zhangjinke/Embedded-Tools-Hardware/Pictures/IMG_20241031_213614.jpg

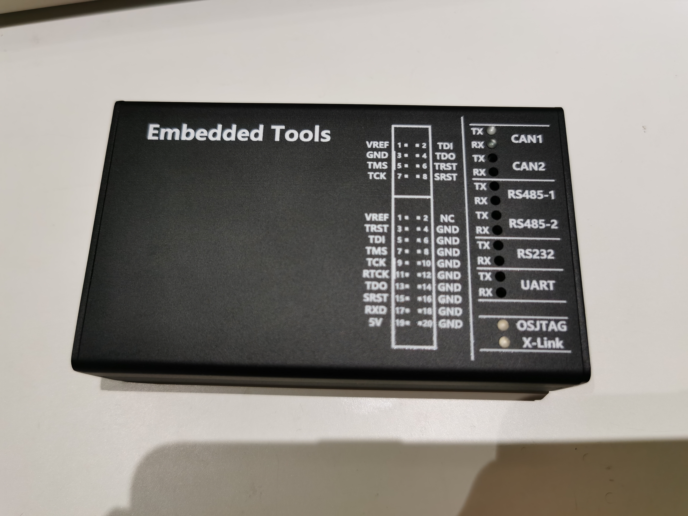
Pictures/IMG_20241031_213614.jpg
