zhangjinke/Embedded-Tools-Hardware/Pictures/IMG_20241031_214249.jpg

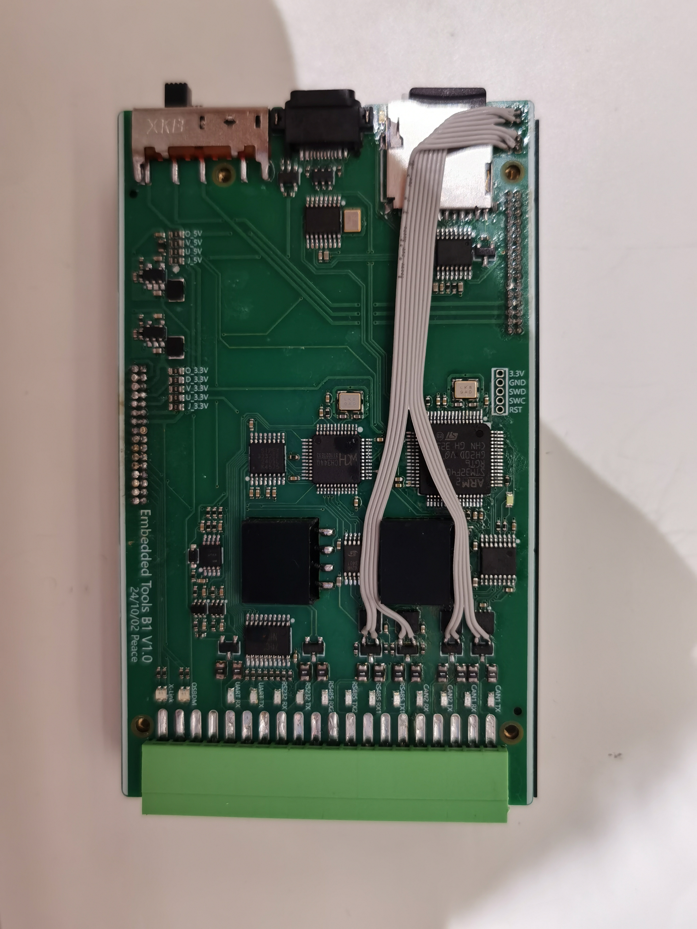
Pictures/IMG_20241031_214249.jpg
