zhangjinke/Embedded-Tools-Hardware/Pictures/IMG_20241031_214307.jpg

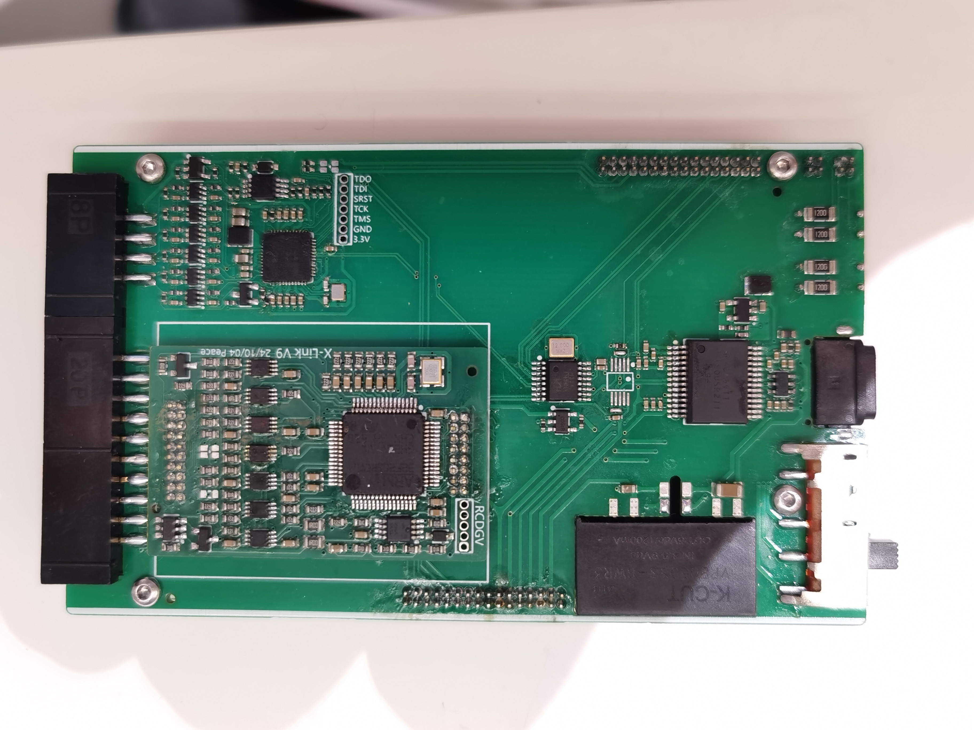
Pictures/IMG_20241031_214307.jpg
