zhangjinke/Embedded-Tools-Hardware/Pictures/IMG_20241031_214337.jpg

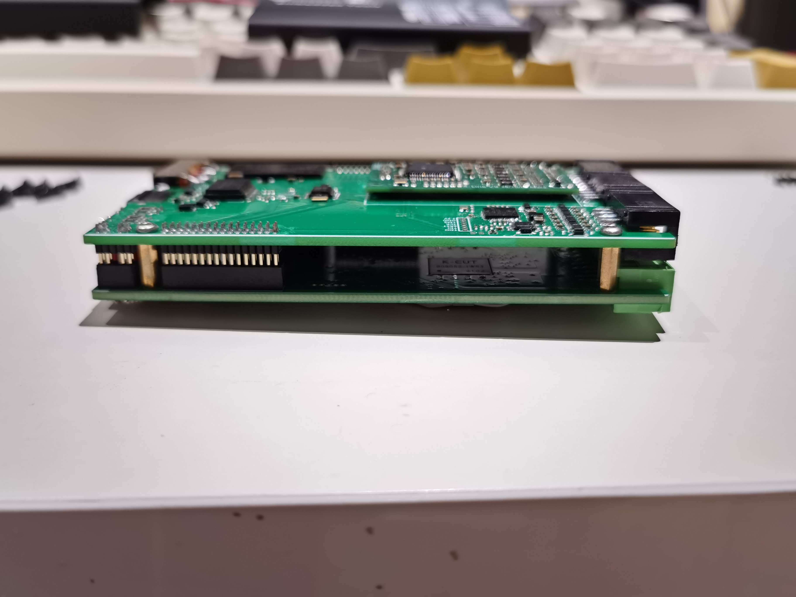
Pictures/IMG_20241031_214337.jpg
