zhangjinke/Embedded-Tools-Hardware/Pictures/IMG_20241110_171348.jpg

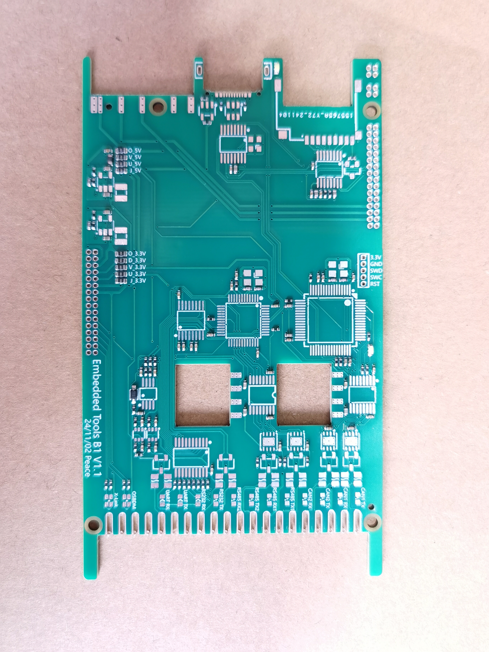
Pictures/IMG_20241110_171348.jpg
