zhangjinke/Embedded-Tools-Hardware/Pictures/IMG_20241110_171440.jpg

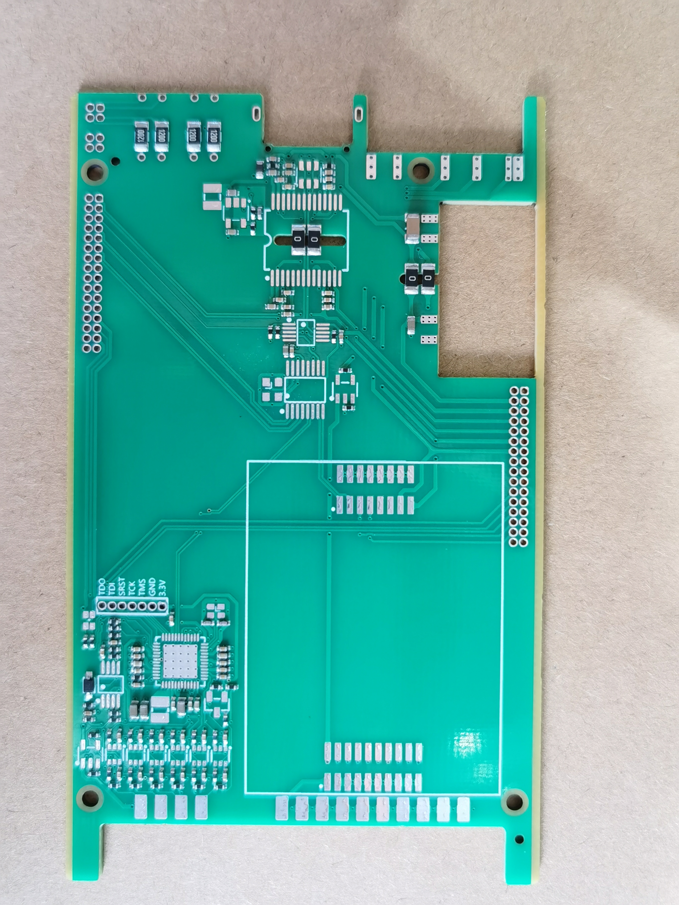
Pictures/IMG_20241110_171440.jpg
