zhangjinke/Embedded-Tools-Hardware/Pictures/IMG_20241111_111140.jpg

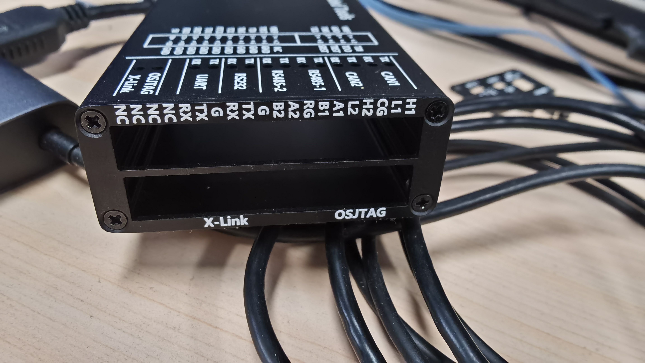
Pictures/IMG_20241111_111140.jpg
