zhangjinke/Embedded-Tools-Hardware/Pictures/IMG_20241116_104931.jpg

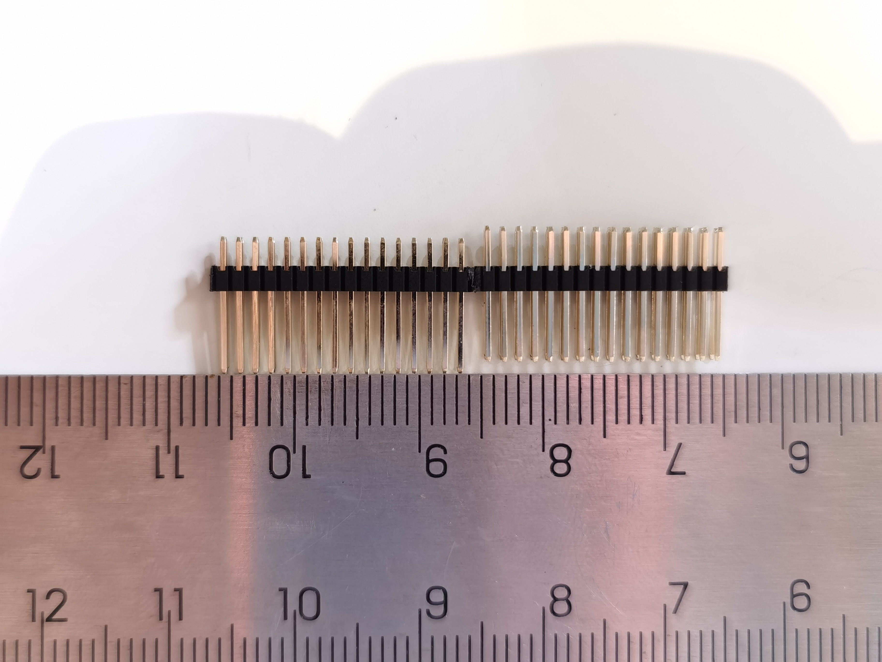
Pictures/IMG_20241116_104931.jpg
