zhangjinke/Embedded-Tools-Hardware/Pictures/IMG_20241116_105723.jpg

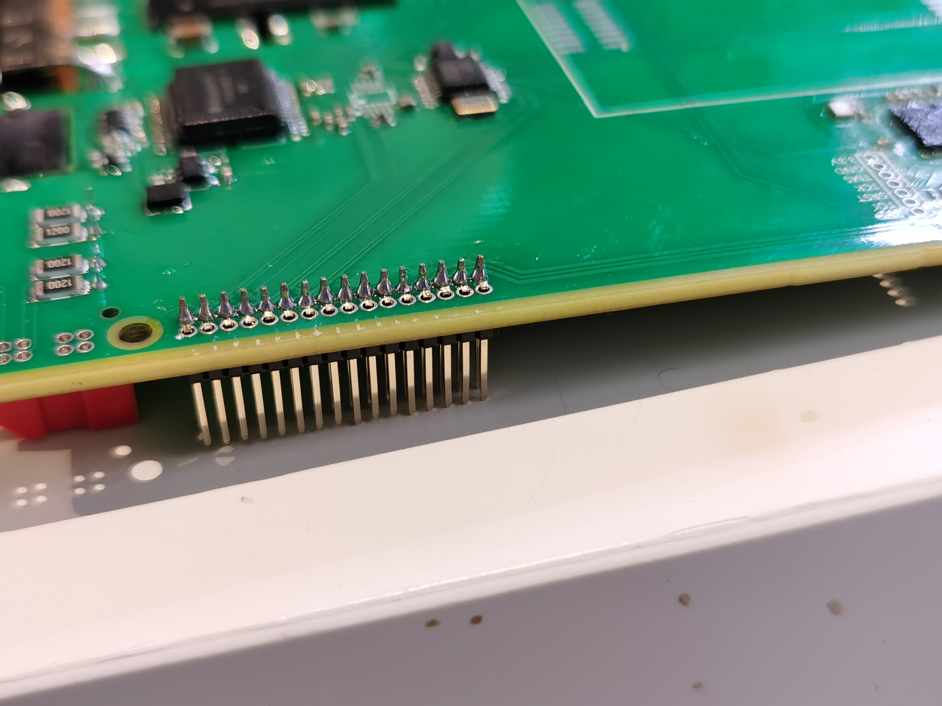
Pictures/IMG_20241116_105723.jpg
