zhangjinke/Embedded-Tools-Hardware/Pictures/IMG_20241116_105740.jpg

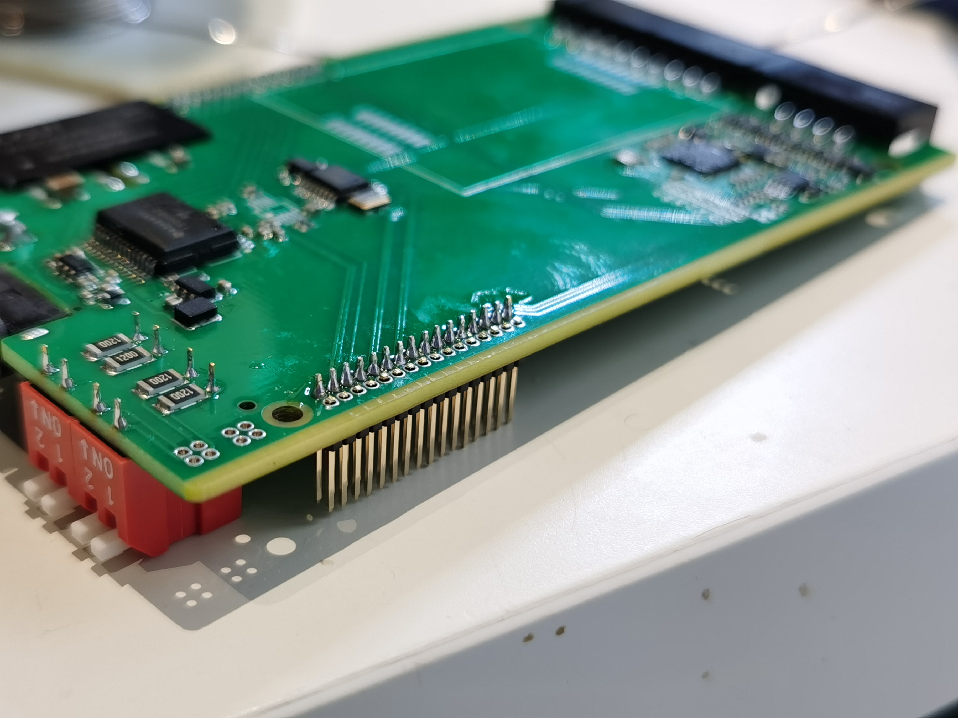
Pictures/IMG_20241116_105740.jpg
