zhangjinke/Embedded-Tools-Hardware/Pictures/IMG_20241116_110107.jpg

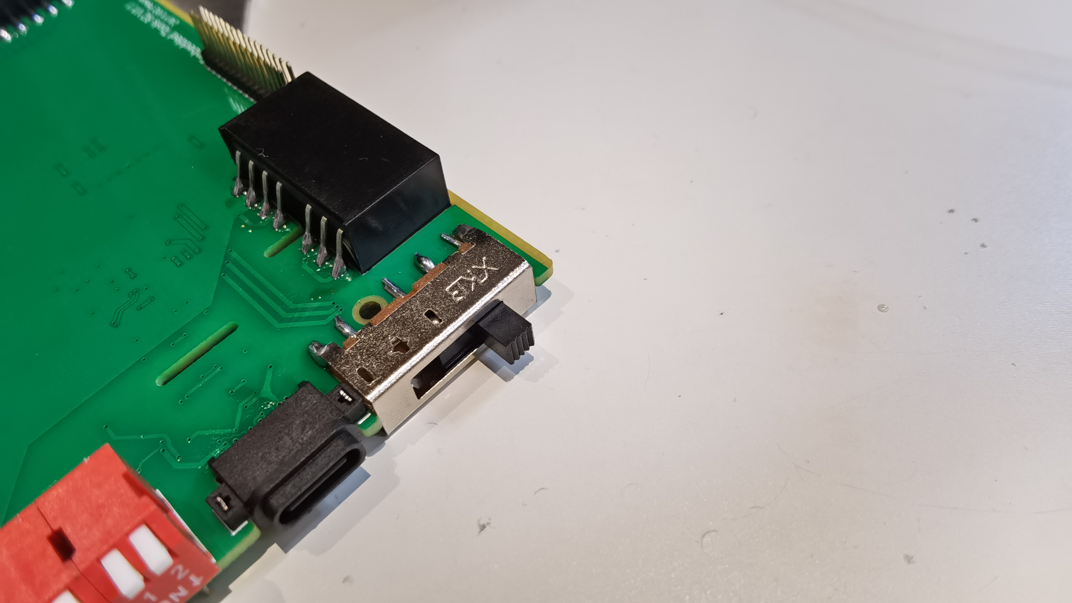
Pictures/IMG_20241116_110107.jpg
