zhangjinke/Embedded-Tools-Hardware/Pictures/IMG_20241116_110145.jpg

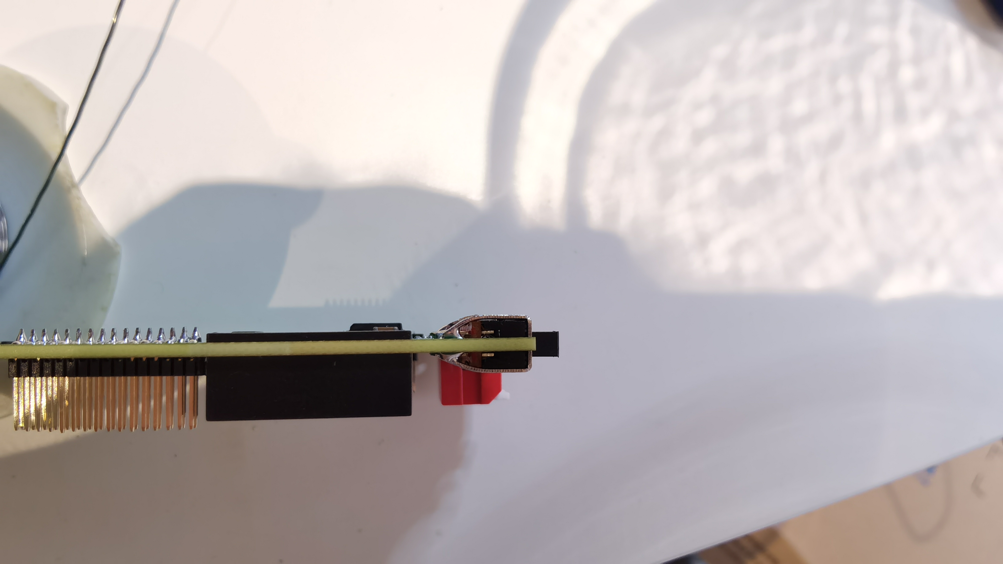
Pictures/IMG_20241116_110145.jpg
