zhangjinke/Embedded-Tools-Hardware/Pictures/IMG_20241118_211116.jpg

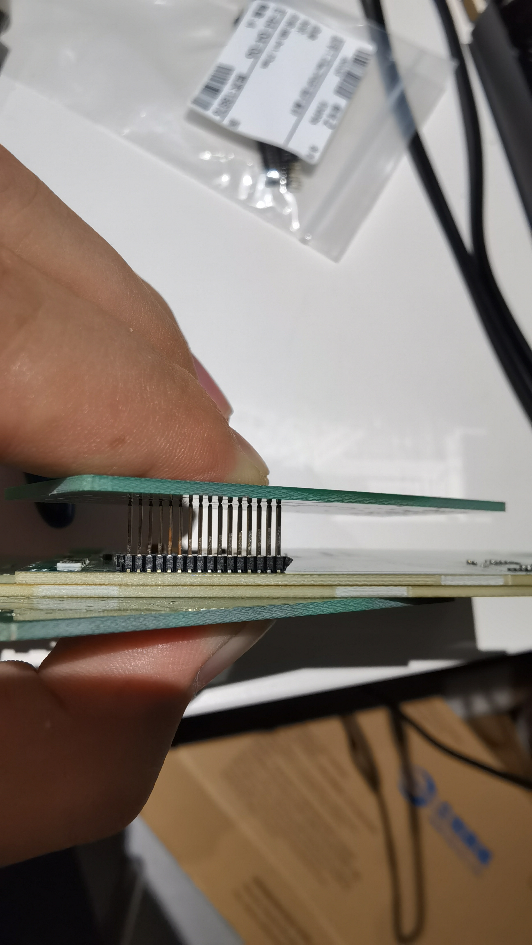
Pictures/IMG_20241118_211116.jpg
