zhangjinke/Embedded-Tools-Hardware/Pictures/IMG_20241118_215939.jpg

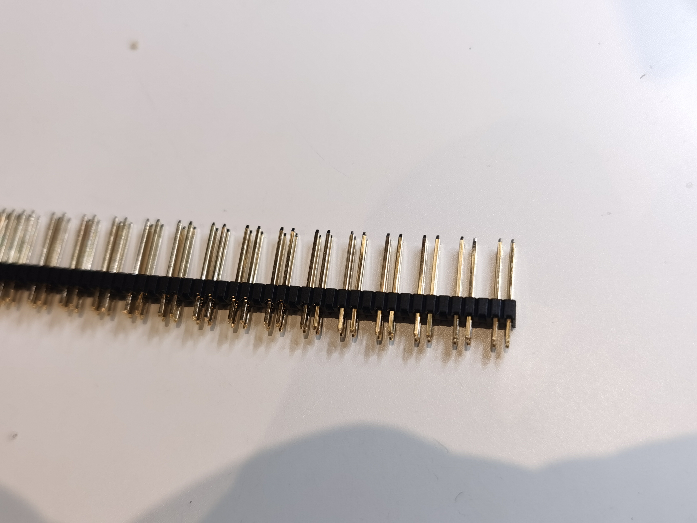
Pictures/IMG_20241118_215939.jpg
