zhangjinke/Embedded-Tools-Hardware/Pictures/IMG_20241124_105456.jpg

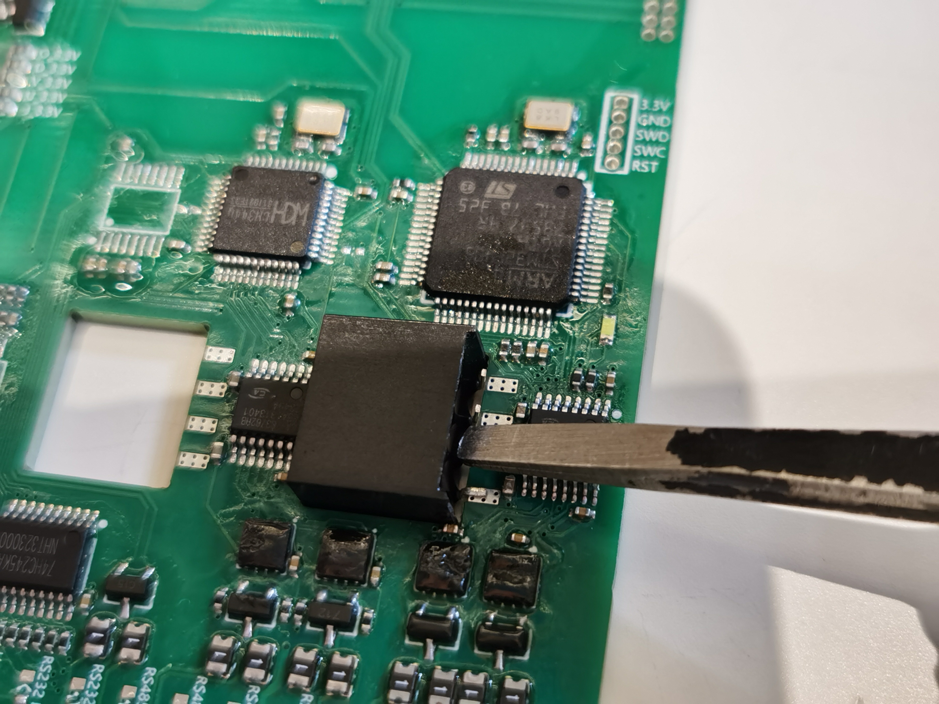
Pictures/IMG_20241124_105456.jpg
