zhangjinke/Embedded-Tools-Hardware/Pictures/IMG_20241124_105819.jpg

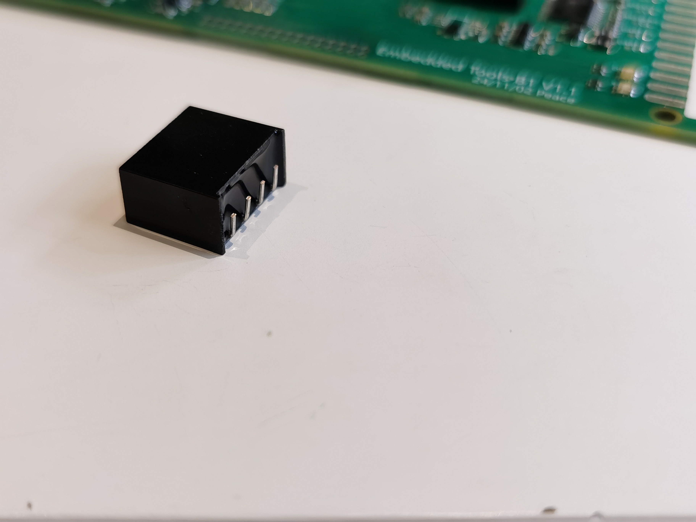
Pictures/IMG_20241124_105819.jpg
