zhangjinke/Embedded-Tools-Hardware/Pictures/IMG_20241128_220155.jpg

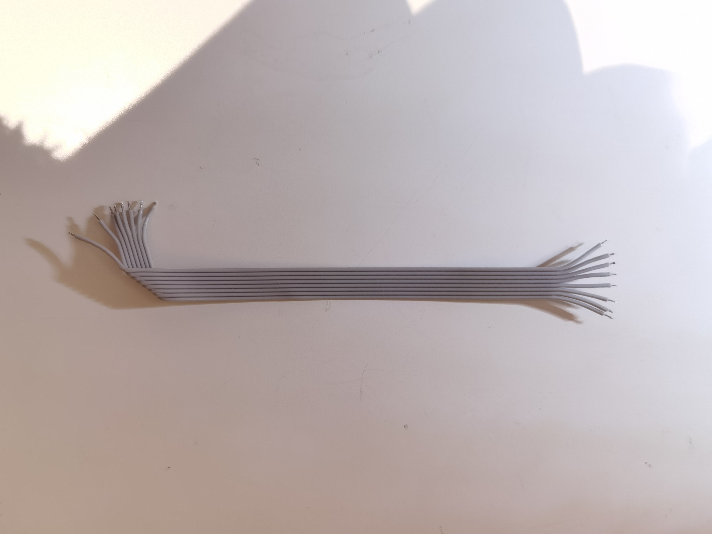
Pictures/IMG_20241128_220155.jpg
