zhangjinke/Embedded-Tools-Hardware/Pictures/IMG_20241128_221212.jpg

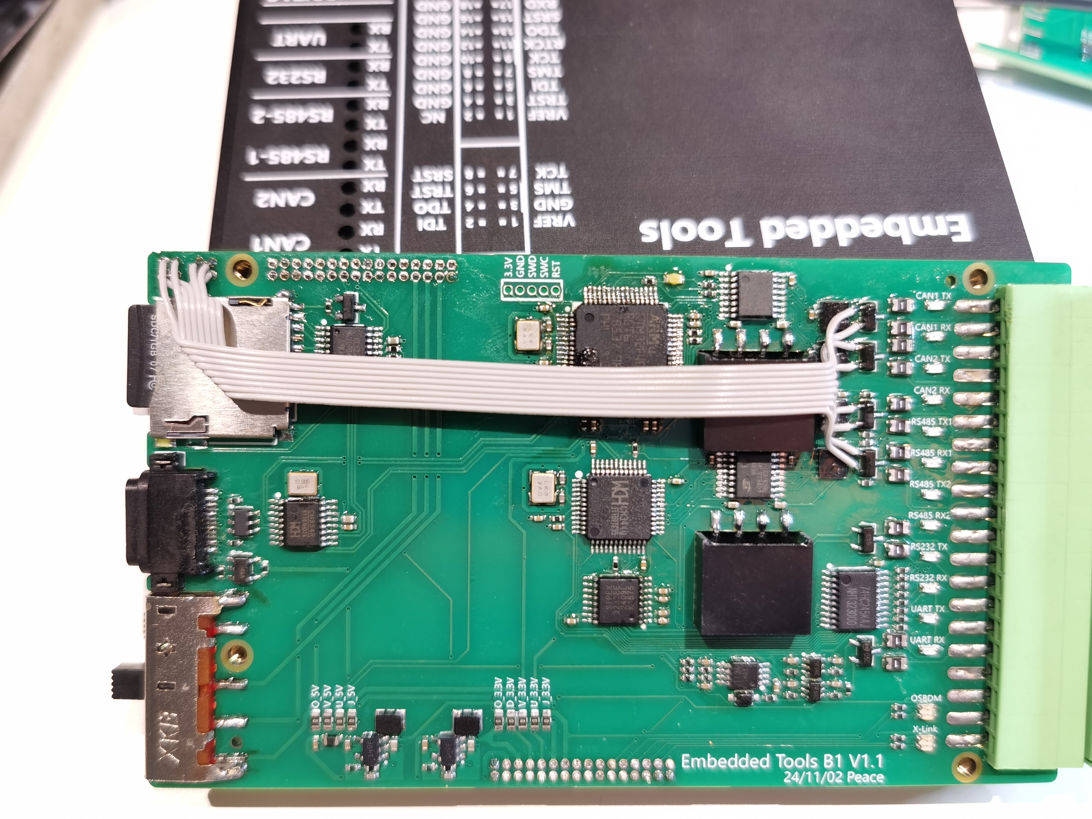
Pictures/IMG_20241128_221212.jpg
