zhangjinke/Embedded-Tools-Hardware/Pictures/IMG_20241128_221221.jpg

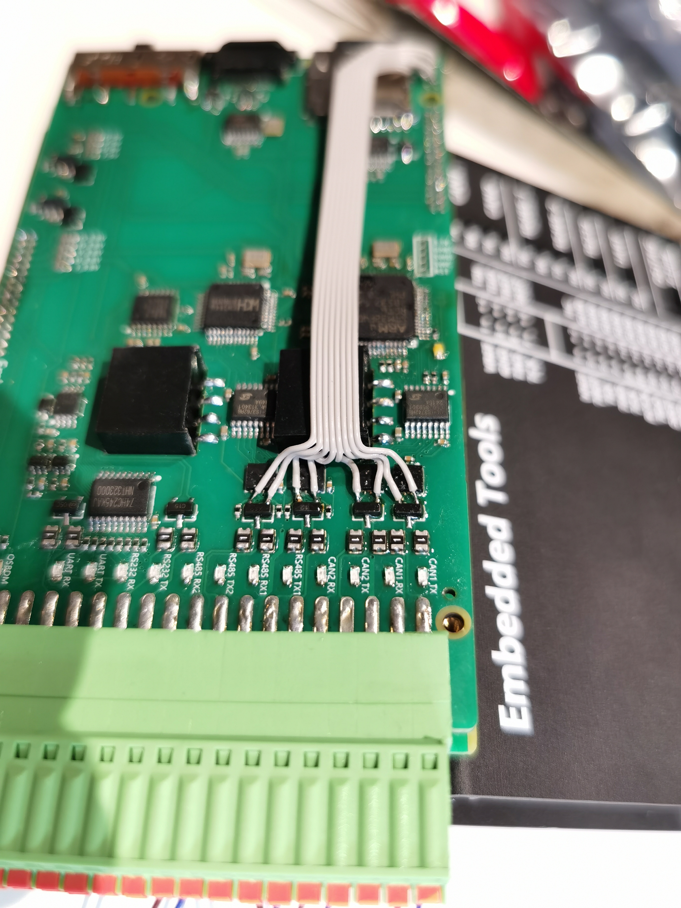
Pictures/IMG_20241128_221221.jpg
