zhangjinke/Embedded-Tools-Hardware/Pictures/IMG_20241128_221230.jpg

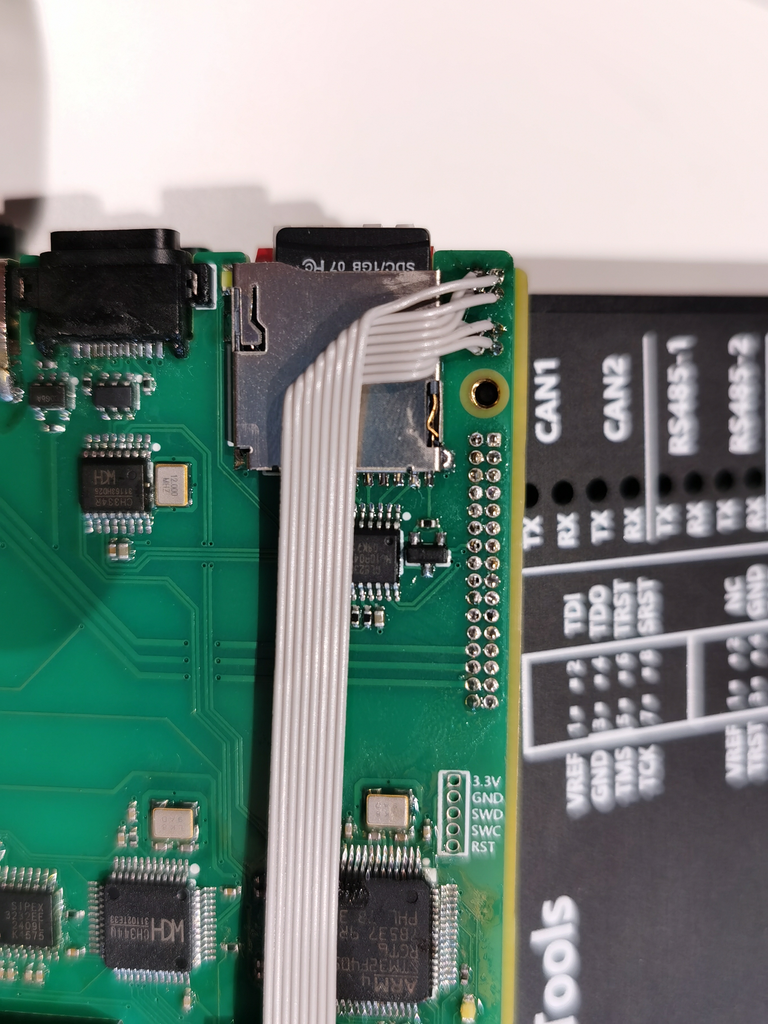
Pictures/IMG_20241128_221230.jpg
