zhangjinke/Embedded-Tools-Hardware/Pictures/IMG_20241128_222254.jpg

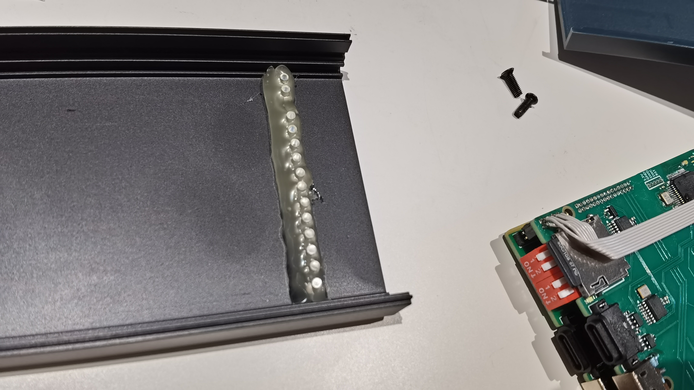
Pictures/IMG_20241128_222254.jpg
