zhangjinke/Embedded-Tools-Hardware/Pictures/IMG_20241128_222530.jpg

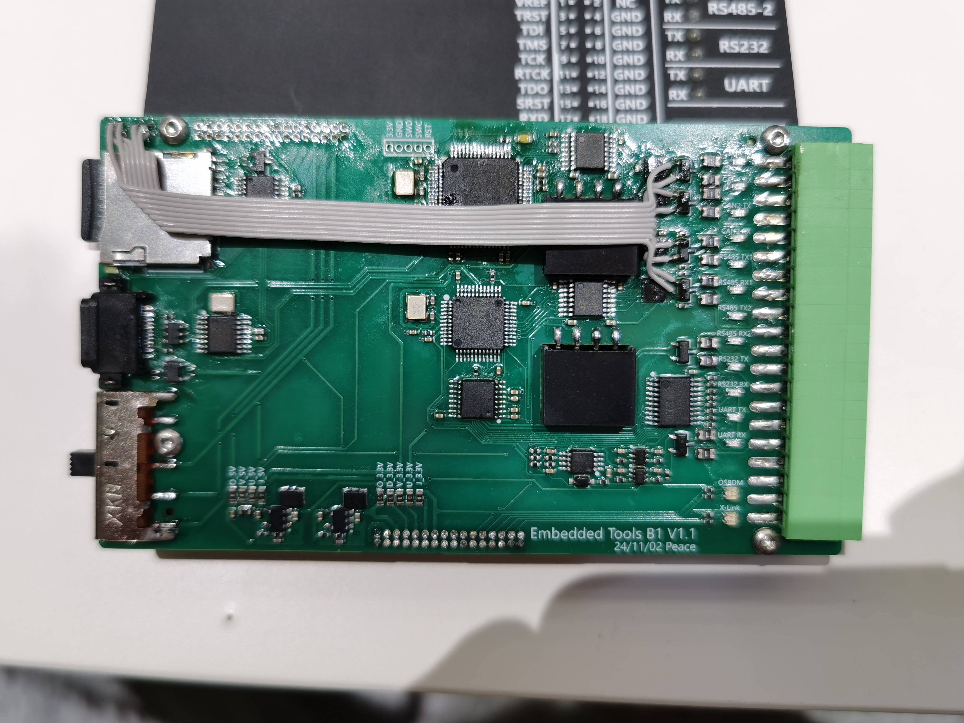
Pictures/IMG_20241128_222530.jpg
