zhangjinke/Embedded-Tools-Hardware/Pictures/IMG_20241128_222554.jpg

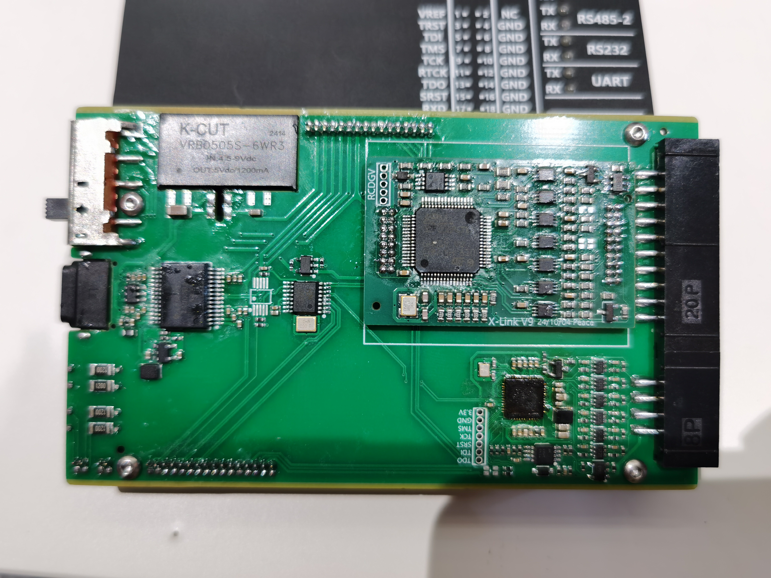
Pictures/IMG_20241128_222554.jpg
