zhangjinke/Embedded-Tools-Hardware/Pictures/IMG_20241128_223136.jpg

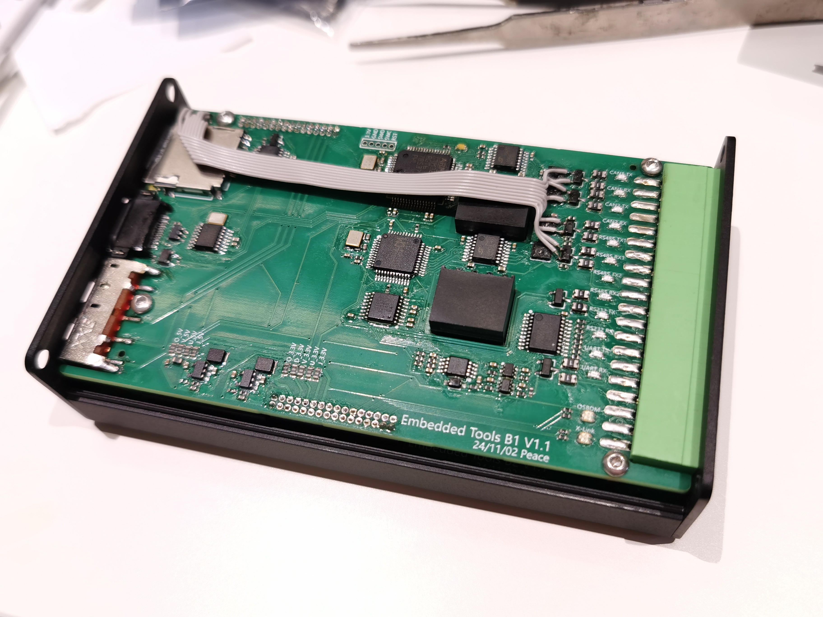
Pictures/IMG_20241128_223136.jpg
